shapoco/xiamocon/cpp/platform/impl/esp32s3_pio_arduino/src/pins.cpp

#include "xmc/pins.hpp"

const int XMC_PIN_I2C_SDA = 5;
const int XMC_PIN_I2C_SCL = 6;
const int XMC_PIN_SPI_MOSI = 9;
const int XMC_PIN_SPI_MISO = 8;
const int XMC_PIN_SPI_SCK = 7;
const int XMC_PIN_DISPLAY_CS = 4;
const int XMC_PIN_DISPLAY_DC = 3;
const int XMC_PIN_TFCARD_CS = 43;
const int XMC_PIN_AUDIO_OUT = 44;
const int XMC_PIN_POWER_BUTTON = 2;
const int XMC_PIN_GPIO_0 = 1;
