shapoco/xiamocon/cpp/platform/impl/rp2350_pico_sdk/src/i2c.cpp

#include "xmc/i2c.hpp"
#include "xmc/gpio.hpp"
#include "xmc/pins.hpp"
#include "xmc/semaphore.hpp"
#include "xmc/timer.hpp"

#include <hardware/gpio.h>
#include <hardware/i2c.h>
#include <pico/stdlib.h>

namespace xmc::i2c {

static i2c_inst_t *const i2cInst = i2c1;
static Semaphore *semaphore = nullptr;
bool isInited = false;

uint32_t getPreferredFrequency(Chipset device) {
  switch (device) {
    default: return 400000;
  }
}

XmcStatus init() {
  resetBus();
  i2c_init(i2cInst, getPreferredFrequency(Chipset::IO_EXPANDER));
  gpio_set_function(XMC_PIN_I2C_SDA, GPIO_FUNC_I2C);
  gpio_set_function(XMC_PIN_I2C_SCL, GPIO_FUNC_I2C);
  gpio_pull_up(XMC_PIN_I2C_SDA);
  gpio_pull_up(XMC_PIN_I2C_SCL);
  isInited = true;
  if (semaphore) delete semaphore;
  semaphore = new Semaphore();
  if (!semaphore->isInitialized()) {
    XMC_ERR_RET(XMC_ERR_SEMAPHORE_INIT_FAILED);
  }
  return XMC_OK;
}

void deinit() {
  i2c_deinit(i2cInst);
  gpio_deinit(XMC_PIN_I2C_SDA);
  gpio_deinit(XMC_PIN_I2C_SCL);
  isInited = false;
  if (semaphore) {
    delete semaphore;
    semaphore = nullptr;
  }
}

bool tryLock() {
  if (!semaphore) return true;
  return semaphore->tryTake();
}

XmcStatus unlock() {
  if (semaphore) semaphore->give();
  return XMC_OK;
}

XmcStatus setBaudrate(uint32_t baudrate) {
  i2c_set_baudrate(i2cInst, baudrate);
  return XMC_OK;
}

XmcStatus resetBus() {
  XmcStatus sts = XMC_OK;

  bool reInit = isInited;
  if (reInit) {
    deinit();
  }

  gpio::setDir(XMC_PIN_I2C_SDA, false);
  gpio::setDir(XMC_PIN_I2C_SCL, false);
  int numRetriesLeft = BUS_RESET_RETRY_COUNT;
  while (--numRetriesLeft >= 0) {
    if (!gpio::read(XMC_PIN_I2C_SDA)) {
      // Clock the bus until the slave releases the SDA line
      gpio::setDir(XMC_PIN_I2C_SCL, true);
      gpio::write(XMC_PIN_I2C_SCL, false);
      sleepUs(100);
      bool success = false;
      for (int i = 0; i < 9; i++) {
        gpio::write(XMC_PIN_I2C_SCL, true);
        sleepUs(100);
        gpio::write(XMC_PIN_I2C_SCL, false);
        sleepUs(100);
        if (gpio::read(XMC_PIN_I2C_SDA)) {
          success = true;
          break;
        }
      }
      // Send a stop condition
      gpio::write(XMC_PIN_I2C_SCL, false);
      gpio::write(XMC_PIN_I2C_SDA, false);
      gpio::setDir(XMC_PIN_I2C_SCL, true);
      gpio::setDir(XMC_PIN_I2C_SDA, true);
      sleepUs(100);
      gpio::setDir(XMC_PIN_I2C_SCL, false);
      sleepUs(100);
      gpio::setDir(XMC_PIN_I2C_SDA, false);
      sleepUs(100);
      if (success) {
        break;
      }
    }
  }
  if (numRetriesLeft < 0) {
    sts = XMC_ERR_I2C_BUS_RESET_FAILED;
  }

  if (reInit) {
    sts = init();
  }
  return sts;
}

XmcStatus writeBlocking(uint8_t devAddr, const uint8_t *data, uint32_t size,
                        bool nostop) {
  int n = i2c_write_blocking(i2cInst, devAddr, data, size, nostop);
  if (n != (int)size) {
    XMC_ERR_RET(XMC_ERR_I2C_WRITE_FAILED);
  }
  return XMC_OK;
}

XmcStatus readBlocking(uint8_t devAddr, uint8_t *data, uint32_t size,
                       bool nostop) {
  int n = i2c_read_blocking(i2cInst, devAddr, data, size, nostop);
  if (n != (int)size) {
    XMC_ERR_RET(XMC_ERR_I2C_READ_FAILED);
  }
  return XMC_OK;
}

}  // namespace xmc::i2c
