shapoco/xiamocon/cpp/platform/impl/rp2350_pico_sdk/src/pins.cpp

#include "xmc/pins.hpp"

const int XMC_PIN_I2C_SDA = 6;
const int XMC_PIN_I2C_SCL = 7;
const int XMC_PIN_SPI_MOSI = 3;
const int XMC_PIN_SPI_MISO = 4;
const int XMC_PIN_SPI_SCK = 2;
const int XMC_PIN_DISPLAY_CS = 5;
const int XMC_PIN_DISPLAY_DC = 28;
const int XMC_PIN_TFCARD_CS = 0;
const int XMC_PIN_AUDIO_OUT = 1;
const int XMC_PIN_POWER_BUTTON = 27;
const int XMC_PIN_GPIO_0 = 26;
