shapoco/xiamocon/cpp/platform/impl/rp2350_pico_sdk/src/timer.cpp

#include "xmc/timer.hpp"
#include "xmc/heap.hpp"

#include <pico/stdlib.h>
#include <stdlib.h>

namespace xmc {

struct RepeatingTimerHwRp {
  repeating_timer_t *timer;
  TimerCallback cb;
  void *context;
};

static bool repeatingTimerCallback(repeating_timer_t *rt);

uint64_t getTimeMs() { return to_ms_since_boot(get_absolute_time()); }
uint64_t getTimeUs() { return to_us_since_boot(get_absolute_time()); }
void sleepMs(uint32_t ms) { sleep_ms(ms); }
void sleepUs(uint32_t us) { sleep_us(us); }

RepeatingTimer::RepeatingTimer() {
  RepeatingTimerHwRp *hw =
      (RepeatingTimerHwRp *)xmcMalloc(sizeof(RepeatingTimerHwRp), XMC_HEAP_CAP_DMA);

  if (!hw) return;
  handle = hw;
  hw->timer = (repeating_timer_t *)xmcMalloc(sizeof(repeating_timer_t),
                                             XMC_HEAP_CAP_DMA);
}

RepeatingTimer::~RepeatingTimer() {
  if (handle) {
    RepeatingTimerHwRp *hw = (RepeatingTimerHwRp *)handle;
    if (hw->timer) {
      cancel_repeating_timer(hw->timer);
      xmcFree(hw->timer);
    }
    xmcFree(handle);
    handle = nullptr;
  }
}

XmcStatus RepeatingTimer ::startMs(uint32_t intervalMs, TimerCallback cb,
                                   void *context) {
  if (!handle) XMC_ERR_RET(XMC_ERR_NOT_INITIALIZED);
  RepeatingTimerHwRp *hw = (RepeatingTimerHwRp *)handle;
  hw->cb = cb;
  hw->context = context;
  if (!add_repeating_timer_ms(intervalMs, repeatingTimerCallback, hw,
                              hw->timer)) {
    xmcFree(handle);
    return XMC_ERR_TIMER_REPEATING_TIMER_INIT_FAILED;
  }
  return XMC_OK;
}

void RepeatingTimer::cancel() {
  if (!handle) return;
  RepeatingTimerHwRp *hw = (RepeatingTimerHwRp *)handle;
  if (!hw->timer) return;
  cancel_repeating_timer(hw->timer);
}

static bool repeatingTimerCallback(repeating_timer_t *rt) {
  RepeatingTimerHwRp *hw = (RepeatingTimerHwRp *)rt->user_data;
  return hw->cb(hw->context);
}

}  // namespace xmc
