shapoco/xiamocon/cpp/example/imu_demo/include/earth_cloud.hpp

#ifndef EARTH_CLOUD_HPP
#define EARTH_CLOUD_HPP

#include "xmc/gfx.hpp"

static const uint16_t earthCloudData[] = {
    0xBBFF, 0xBBEF, 0xAAEF, 0xAAEF, 0x88EF, 0x88DF, 0x66EF, 0x66DF,
    0x55DF, 0x55DF, 0x55DF, 0x55DF, 0x55DF, 0x66DF, 0x55DF, 0x66DF,
    0x55DF, 0x55DF, 0x55DF, 0x44DF, 0x55DF, 0x44DF, 0x44DF, 0x44DF,
    0x44DF, 0x44DF, 0x44DF, 0x44DF, 0x44DF, 0x55DF, 0x55DF, 0x55DF,
    0x55DF, 0x55DF, 0x56DF, 0x66DF, 0x66DF, 0x66DF, 0x66DF, 0x66DF,
    0x56DF, 0x55DF, 0x55DF, 0x55DF, 0x45DF, 0x44DF, 0x44DF, 0x34CF,
    0x33DF, 0x22CF, 0x22CF, 0x11CF, 0x00CF, 0x00CF, 0x00CF, 0x00CF,
    0x00CF, 0x00CF, 0x00CF, 0x00CF, 0x00CF, 0x00CF, 0x00CF, 0x00CF,
    0x00CF, 0x00CF, 0x00CF, 0x00CF, 0x11CF, 0x00CF, 0x11CF, 0x22CF,
    0x33DF, 0x44DF, 0x55DF, 0x66DF, 0x66DF, 0x77EF, 0x88DF, 0x77EF,
    0x88DF, 0x77EF, 0x77DF, 0x77EF, 0x77DF, 0x77DF, 0x66DF, 0x66DF,
    0x55DF, 0x55DF, 0x55DF, 0x55DF, 0x55DF, 0x55DF, 0x55DF, 0x55DF,
    0x66DF, 0x55DF, 0x66DF, 0x66DF, 0x66DF, 0x66DF, 0x66DF, 0x67DF,
    0x76EF, 0x67DF, 0x77DF, 0x77EF, 0x77DF, 0x77DF, 0x77EF, 0x66DF,
    0x77DF, 0x66DF, 0x66DF, 0x56DF, 0x55DF, 0x55DF, 0x55DF, 0x55DF,
    0x55DF, 0x55DF, 0x55DF, 0x55DF, 0x55DF, 0x55DF, 0x56DF, 0x65DF,
    0x55DF, 0x56DF, 0x55DF, 0x55DF, 0x44DF, 0x45DF, 0x44DF, 0x44DF,
    0x44DF, 0x44DF, 0x44DF, 0x44DF, 0x44DF, 0x44DF, 0x44DF, 0x44DF,
    0x44DF, 0x44DF, 0x44DF, 0x44DF, 0x44DF, 0x44DF, 0x45DF, 0x54DF,
    0x45DF, 0x55DF, 0x55DF, 0x55DF, 0x55DF, 0x55DF, 0x45DF, 0x55DF,
    0x55DF, 0x45DF, 0x55DF, 0x55DF, 0x55DF, 0x55DF, 0x55DF, 0x55DF,
    0x56DF, 0x65DF, 0x56DF, 0x55DF, 0x55DF, 0x55DF, 0x55DF, 0x55DF,
    0x45DF, 0x55DF, 0x55DF, 0x55DF, 0x55DF, 0x66DF, 0x55DF, 0x66DF,
    0x56DF, 0x66DF, 0x66DF, 0x66DF, 0x77EF, 0x77DF, 0x77EF, 0x77DF,
    0x78EF, 0x77DF, 0x77EF, 0x77DF, 0x67DF, 0x76DF, 0x67EF, 0x76DF,
    0x77DF, 0x77EF, 0x77DF, 0x77EF, 0x77DF, 0x78EF, 0x87DF, 0x78EF,
    0x88DF, 0x88EF, 0x99EF, 0x99EF, 0x99EF, 0xAAEF, 0xAAEF, 0xAAEF,
    0xAAEF, 0xBBEF, 0xAAEF, 0xBBEF, 0xAAEF, 0xAAEF, 0xAAEF, 0xABEF,
    0xBAEF, 0xBBEF, 0xBCFF, 0xCCEF, 0xCCFF, 0xDDFF, 0xCCEF, 0xDDFF,
    0xCCFF, 0xCCEF, 0xCCFF, 0xBBEF, 0xBBFF, 0xCCEF, 0xBBEF, 0xCCFF,
    0xBBEF, 0xCCFF, 0xCCEF, 0xCCFF, 0xCCEF, 0xCCFF, 0xBBEF, 0xCCFF,
    0xBBEF, 0xBBEF, 0xBBFF, 0xBBEF, 0xBBEF, 0xCCFF, 0xBBEF, 0xCCFF,
    0xCCEF, 0xCCEF, 0xBBEF, 0xAAEF, 0x99EF, 0x77DF, 0x66DF, 0x55DF,
    0x44CF, 0x44DF, 0x44CF, 0x55DF, 0x55DF, 0x55DF, 0x66DF, 0x55DF,
    0x66DF, 0x55DF, 0x44CF, 0x44DF, 0x44CF, 0x44CF, 0x55DF, 0x44CF,
    0x55DF, 0x55CF, 0x44CF, 0x55DF, 0x55CF, 0x55DF, 0x77DF, 0x88DF,
    0x88EF, 0x99DF, 0x99EF, 0x99EF, 0xAAEF, 0xAAEF, 0xAAEF, 0xAAEF,
    0xAAEF, 0xAAEF, 0x99EF, 0x99EF, 0x89DF, 0x88DF, 0x88EF, 0x77DF,
    0x77DF, 0x66DF, 0x45DF, 0x33CF, 0x22CF, 0x11CF, 0x11CF, 0x00BF,
    0x00CF, 0x00BF, 0x00CF, 0x0FFF, 0x0FFF, 0x0FFF, 0x00BF, 0x00CF,
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
};

static inline xmc::Sprite createEarthCloudSprite() {
  return xmc::createSprite4444(
    256,
    128,
    (void *)earthCloudData
  );
}

#endif
