shapoco/xiamocon/cpp/example/imu_demo/include/earth_surface.hpp

#ifndef EARTH_SURFACE_HPP
#define EARTH_SURFACE_HPP

#include "xmc/gfx.hpp"

static const uint16_t earthSurfaceData[] = {
    0x4608, 0x4608, 0x4608, 0x4608, 0x4608, 0x6608, 0x4608, 0x4608,
    0x4608, 0x4608, 0x4608, 0x6608, 0x4608, 0x4608, 0x4608, 0x4608,
    0x4608, 0x6608, 0x4608, 0x4608, 0x4608, 0x4608, 0x4608, 0x6608,
    0x4608, 0x4608, 0x4608, 0x4608, 0x4608, 0x6608, 0x4608, 0x4608,
    0x4608, 0x4608, 0x4608, 0x6608, 0x4608, 0x4608, 0x4608, 0x4608,
    0x4608, 0x6608, 0x4608, 0x4608, 0x4608, 0x4608, 0x4608, 0x6608,
    0x4608, 0x4608, 0x4608, 0x4608, 0x4608, 0x6608, 0x4608, 0x4608,
    0x4608, 0x4608, 0x4608, 0x6608, 0x4608, 0x4608, 0x4608, 0x4608,
    0x4608, 0x6608, 0x4608, 0x4608, 0x4608, 0x4608, 0x4608, 0x6608,
    0x4608, 0x4608, 0x4608, 0x4608, 0x4608, 0x6608, 0x4608, 0x4608,
    0x4608, 0x4608, 0x4608, 0x6608, 0x4608, 0x4608, 0x4608, 0x4608,
    0x4608, 0x6608, 0x4608, 0x4608, 0x4608, 0x4608, 0x4608, 0x6608,
    0x4608, 0x4608, 0x4608, 0x4608, 0x4608, 0x6608, 0x4608, 0x4608,
    0x4608, 0x4608, 0x4608, 0x6608, 0x4608, 0x4608, 0x4608, 0x4608,
    0x4608, 0x6608, 0x4608, 0x4608, 0x4608, 0x4608, 0x4608, 0x6608,
    0x4608, 0x4608, 0x4608, 0x4608, 0x4608, 0x6608, 0x4608, 0x4608,
    0x4608, 0x4608, 0x4608, 0x6608, 0x4608, 0x4608, 0x4608, 0x4608,
    0x4608, 0x6608, 0x4608, 0x4608, 0x4608, 0x4608, 0x4608, 0x6608,
    0x4608, 0x4608, 0x4608, 0x4608, 0x4608, 0x6608, 0x4608, 0x4608,
    0x4608, 0x4608, 0x4608, 0x6608, 0x4608, 0x4608, 0x4608, 0x4608,
    0x4608, 0x6608, 0x4608, 0x4608, 0x4608, 0x4608, 0x4608, 0x6608,
    0x4608, 0x4608, 0x4608, 0x4608, 0x4608, 0x6608, 0x4608, 0x4608,
    0x4608, 0x4608, 0x4608, 0x6608, 0x4608, 0x4608, 0x4608, 0x4608,
    0x4608, 0x6608, 0x4608, 0x4608, 0x4608, 0x4608, 0x4608, 0x6608,
    0x4608, 0x4608, 0x4608, 0x4608, 0x4608, 0x6608, 0x4608, 0x4608,
    0x4608, 0x4608, 0x4608, 0x6608, 0x4608, 0x4608, 0x4608, 0x4608,
    0x4608, 0x6608, 0x4608, 0x4608, 0x4608, 0x4608, 0x4608, 0x6608,
    0x4608, 0x4608, 0x4608, 0x4608, 0x4608, 0x6608, 0x4608, 0x4608,
    0x4608, 0x4608, 0x4608, 0x6608, 0x4608, 0x4608, 0x4608, 0x4608,
    0x4608, 0x6608, 0x4608, 0x4608, 0x4608, 0x4608, 0x4608, 0x6608,
    0x4608, 0x4608, 0x4608, 0x4608, 0x4608, 0x6608, 0x4608, 0x4608,
    0x4608, 0x4608, 0x4608, 0x6608, 0x4608, 0x4608, 0x4608, 0x6610,
    0x4608, 0x6610, 0x6608, 0x6610, 0x4608, 0x6610, 0x4608, 0x6610,
    0x6608, 0x6610, 0x4608, 0x6610, 0x4608, 0x6610, 0x6608, 0x6610,
    0x4608, 0x6610, 0x4608, 0x6610, 0x6608, 0x6610, 0x4608, 0x6610,
    0x4608, 0x6610, 0x6608, 0x6610, 0x4608, 0x6610, 0x4608, 0x6610,
    0x6608, 0x6610, 0x4608, 0x6610, 0x4608, 0x6610, 0x6608, 0x6610,
    0x4608, 0x6610, 0x4608, 0x6610, 0x6608, 0x6610, 0x4608, 0x6610,
    0x4608, 0x6610, 0x6608, 0x6610, 0x4608, 0x6610, 0x4608, 0x6610,
    0x6608, 0x6610, 0x4608, 0x6610, 0x4608, 0x6610, 0x6608, 0x6610,
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
};

static inline xmc::Sprite createEarthSurfaceSprite() {
  return xmc::createSprite565(
    256,
    128,
    (void *)earthSurfaceData
  );
}

#endif
